paaatcha/IEEE-OPEN/larc2013/estrutura/img/polipo1.png

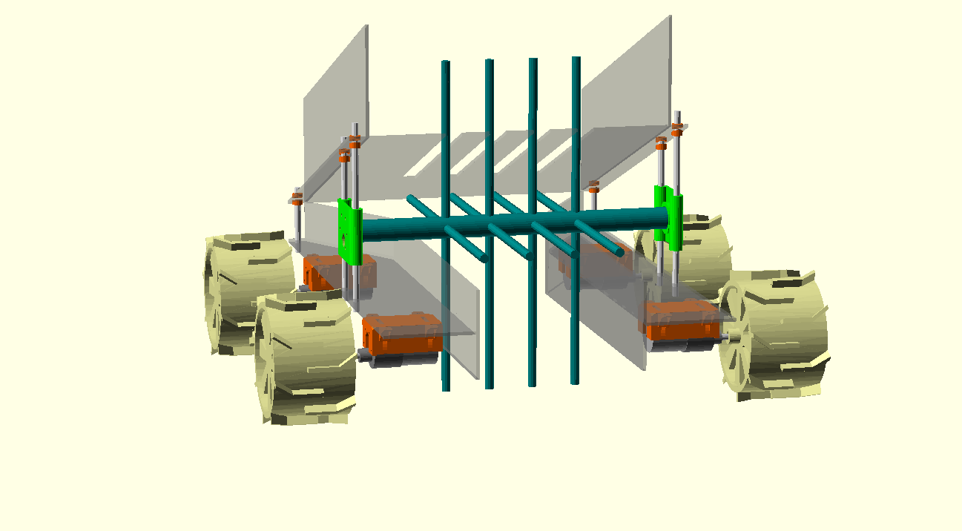
larc2013/estrutura/img/polipo1.png
