paaatcha/IEEE-OPEN/larc2013/estrutura/img/polipo5.png

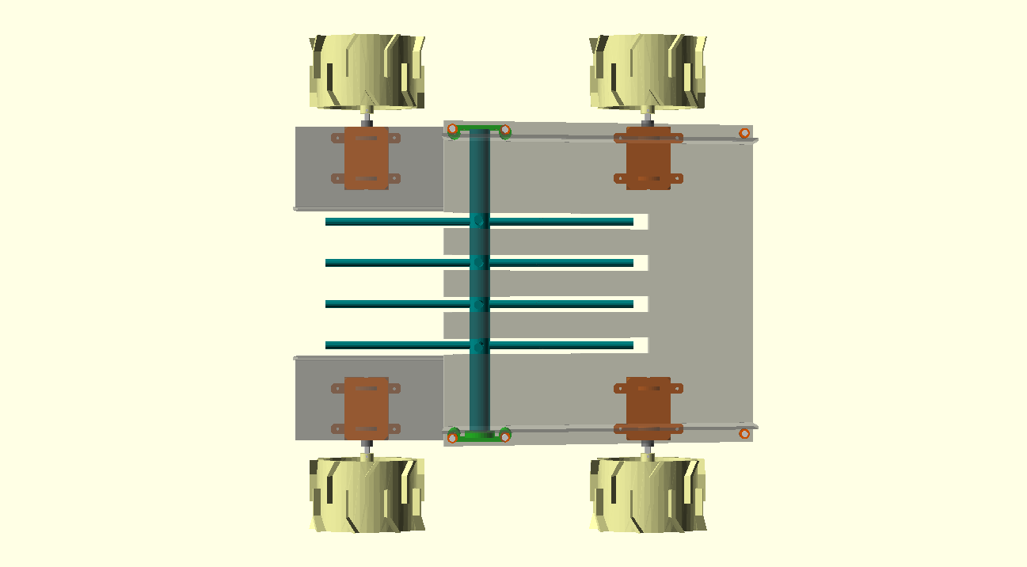
larc2013/estrutura/img/polipo5.png
