paaatcha/IEEE-OPEN/larc2013/estrutura/img/polipo6.png

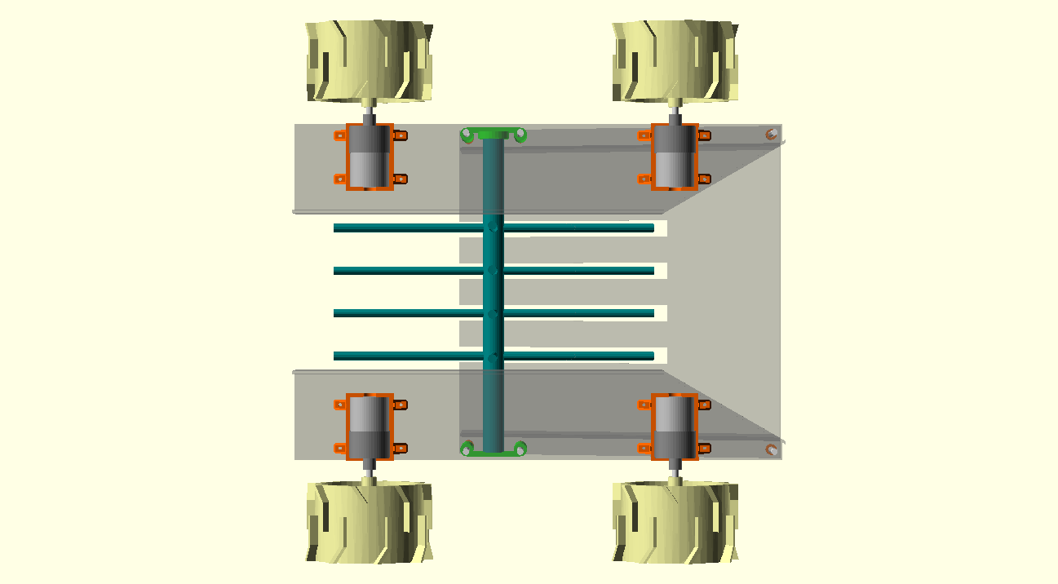
larc2013/estrutura/img/polipo6.png
