paaatcha/IEEE-OPEN/larc2013/estrutura/img/suporteRolamentoVassoura.png

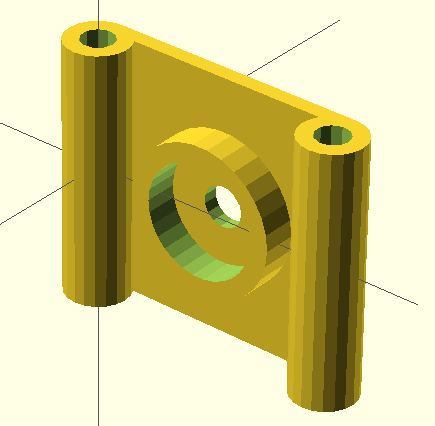
larc2013/estrutura/img/suporteRolamentoVassoura.png
