paaatcha/IEEE-OPEN/larc2013/estrutura/bigBattery.scad

module bigBattery()
{
	color([0.1, 0.1, 0.1])
	{
		cube([172, 34, 60], center=true);
	}
}

bigBattery();
