paaatcha/IEEE-OPEN/larc2013/estrutura/half_moon_3D.scad

include <medidas.scad>
include <half_moon.scad>

module halfMoon3D()
{
	

}
