paaatcha/IEEE-OPEN/larc2013/estrutura/Polipo.scad

include <rampa.scad>

rampa();
