paaatcha/IEEE-OPEN/larc2013/estrutura/RodaRefletida.scad

mirror()
import("/home/erus/Downloads/Roda.stl");
