paaatcha/IEEE-OPEN/larc2013/estrutura/smallBattery.scad

module smallBattery()
{
	color([0.1,0.1,0.1])
	{
		cube([42, 97, 52], center=true);
	}
}

smallBattery();
